EvEdSchob/MotorThrustStand/PiCode/ThrustStand/src/DynoMode.java

/*  Title:  DynoMode.Java
 *  Author: Evan Schober
 *  Email:  evan.e.schober@wmich.edu
 *  Parent Class: ThrustStand.java
 *  Description: Controller class for the dyno mode 
 */

import javafx.fxml.FXML;
import javafx.scene.control.*;
public class DynoMode extends BaseController {
    //Generic controls shared between the lab and dyno scenes
    @FXML private TextField thrustField;
    @FXML private TextField currentField;
    @FXML private TextField voltageField;
    @FXML private TextField incomingAirspeedField;
    @FXML private TextField wakeAirspeedField;
    @FXML private ComboBox<String> thrustUnitCombo;
    @FXML private ComboBox<String> incomingAirspeedUnitCombo;
    @FXML private ComboBox<String> wakeAirspeedUnitCombo;
    @FXML private ComboBox<Integer> bladeCountCombo;
    @FXML private Button tearButton;
    @FXML private ToggleButton holdToggle;
    @FXML private ToggleButton motorToggle;
    @FXML private ToggleButton loggingToggle;
    @FXML private Button returnToMainBtn;

    //Dyno mode specific controls
    @FXML private Slider throttleSlider;
    @FXML private TextField rpmField;

    @FXML
    public void initialize() {
        //System.out.println("DynoMode initializing..."); //Debug
        
        // Initialize shared controls
        sharedElements.initializeControls(
            thrustField,
            tearButton,
            holdToggle,
            thrustUnitCombo,
            incomingAirspeedField,
            wakeAirspeedField,
            incomingAirspeedUnitCombo,
            wakeAirspeedUnitCombo,
            currentField,
            voltageField,
            bladeCountCombo,
            motorToggle,
            loggingToggle
        );

        // Set mode to DYNO
        serialController.setMode("DYNO");
        
        // Add throttle slider listener
        throttleSlider.valueChangingProperty().addListener((obs, wasChanging, isChanging) -> {
            if (!isChanging && motorToggle.isSelected()) {
                // Only send the command when the slider stops moving and motor is on
                serialController.setThrottle((int) throttleSlider.getValue());
            }
        });
        
        // Motor toggle listener
        motorToggle.setOnAction(event -> {
            sharedElements.handleMotorToggle();
        });

        // Add data received listener for telemetry
        serialController.addDataReceivedListener(this::onDataReceived);

        // Other control handlers
        tearButton.setOnAction(e -> sharedElements.handleTearButton());
        holdToggle.setOnAction(e -> sharedElements.handleHoldToggle());
        loggingToggle.setOnAction(e -> sharedElements.handleLoggerToggle());
        
        bladeCountCombo.setOnAction(event -> {
            serialController.setBladeCount(bladeCountCombo.getValue());
        });
    }

    private void onDataReceived(String data) {
        serialController.parseData(data);
    }

    @FXML
    void returnToMainBtn() {
        //System.out.println("Returning to launcher");  //Debug
        try {
            // Turn off motor before returning
            if (motorToggle.isSelected()) {
                serialController.setMotor(false);
                motorToggle.setSelected(false);
            }
            thrustStand.changeScene("fxml/Launcher.fxml");
        } catch (Exception e) {
            e.printStackTrace();
        }
    }
}
